abdulkhan94/HiFi-Audio-Amplifier-PCB_Design-/Documents & Simulations/FDR/proto_v2_1.png

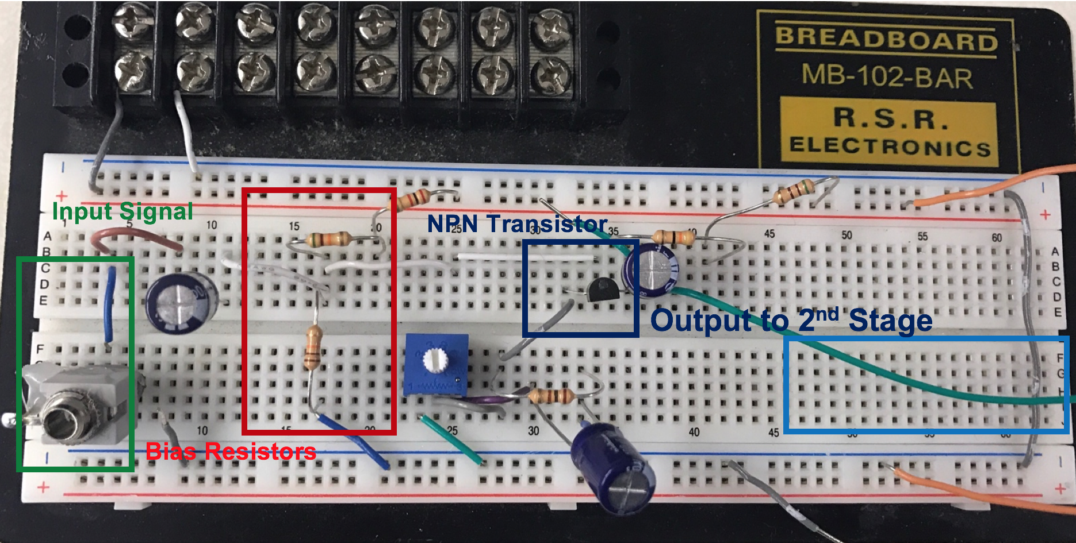
Documents & Simulations/FDR/proto_v2_1.png
