abdulkhan94/HiFi-Audio-Amplifier-PCB_Design-/Documents & Simulations/FDR/FFT_16.png

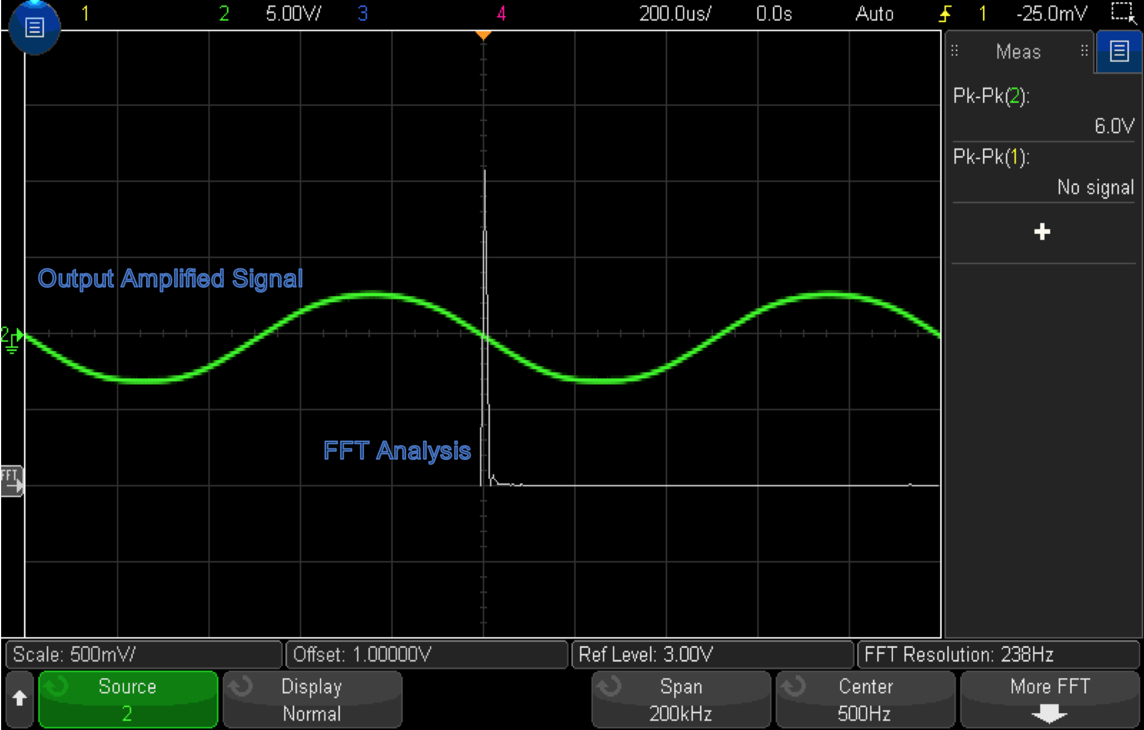
Documents & Simulations/FDR/FFT_16.png
