abdulkhan94/HiFi-Audio-Amplifier-PCB_Design-/Documents & Simulations/FDR/FFT_600.png

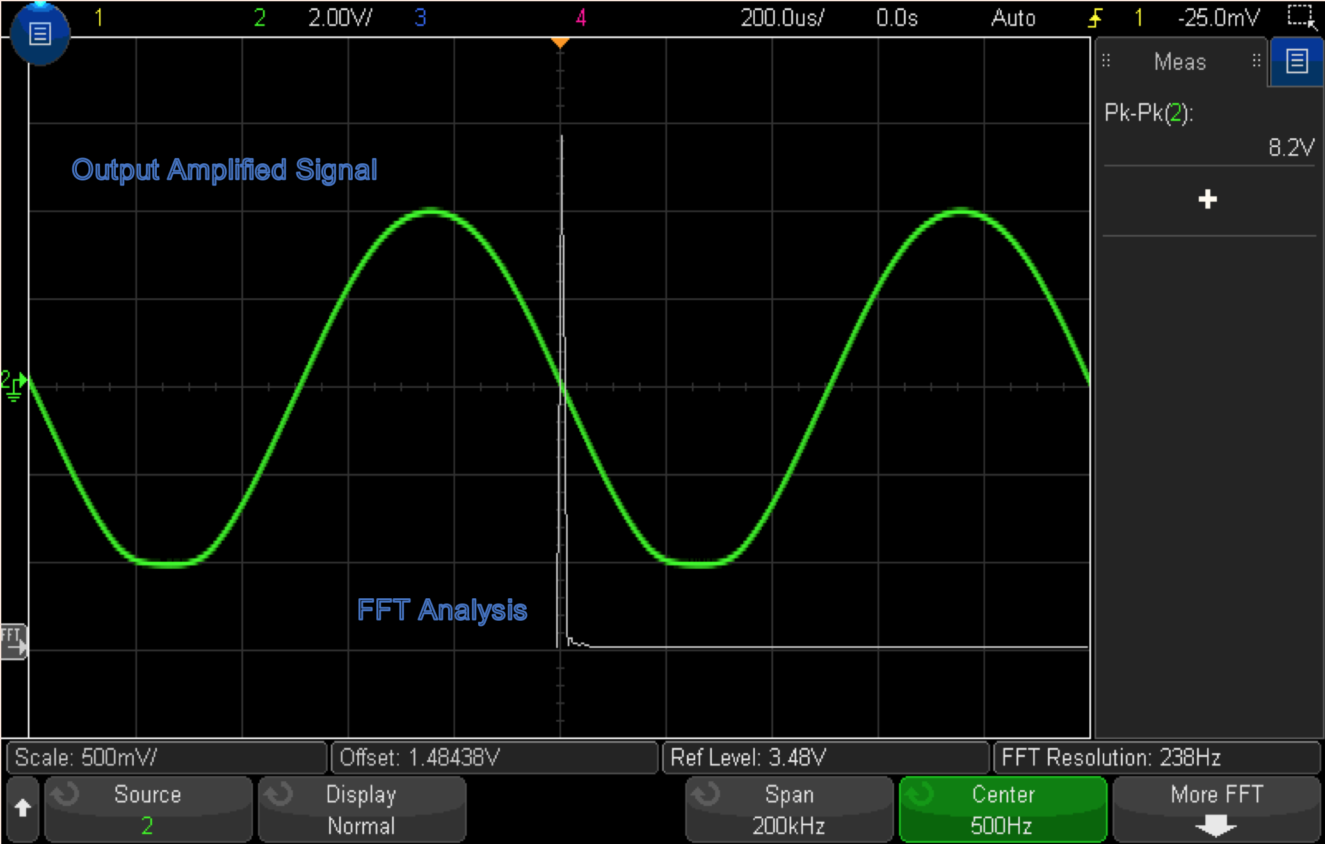
Documents & Simulations/FDR/FFT_600.png
