abdulkhan94/HiFi-Audio-Amplifier-PCB_Design-/Documents & Simulations/FDR/PCB_Final.png

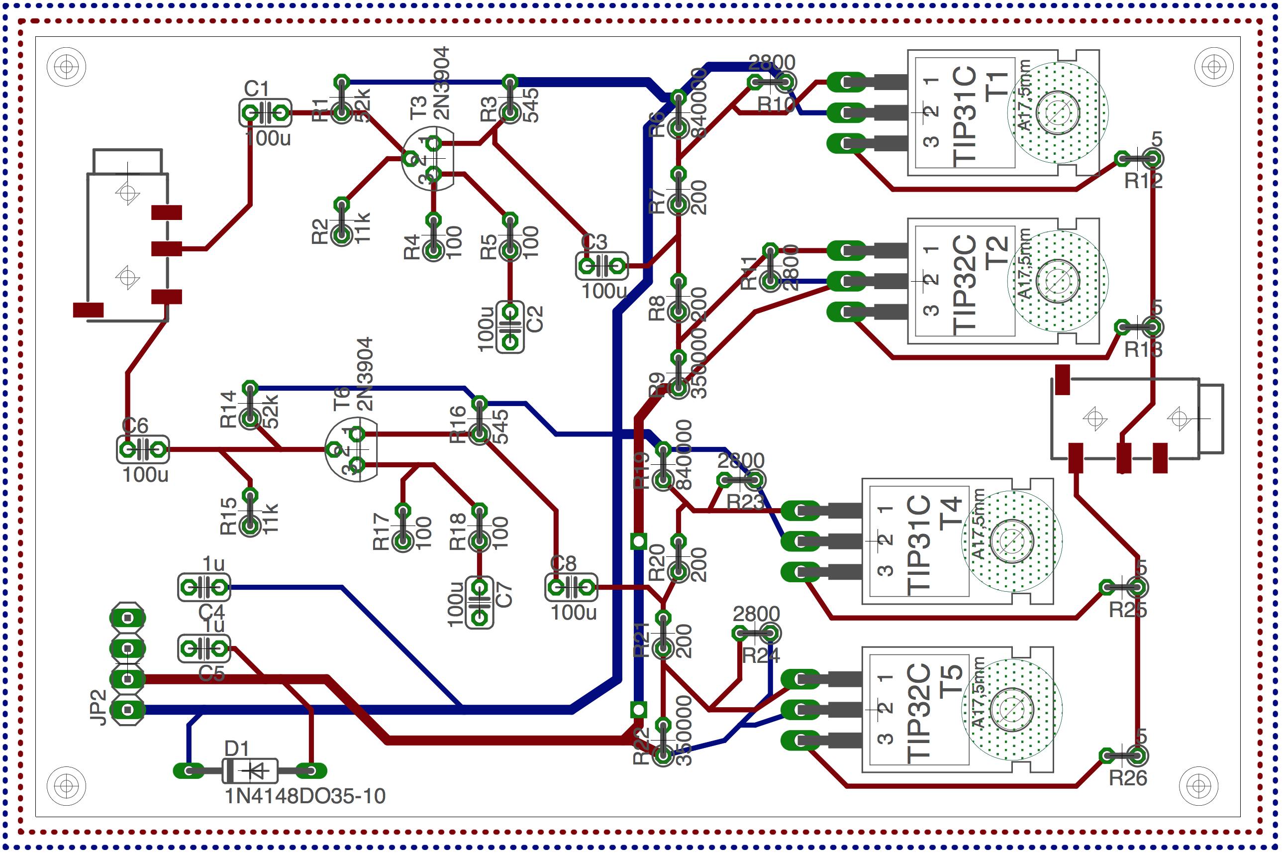
Documents & Simulations/FDR/PCB_Final.png
