abdulkhan94/HiFi-Audio-Amplifier-PCB_Design-/Documents & Simulations/FDR/Power_rails.png

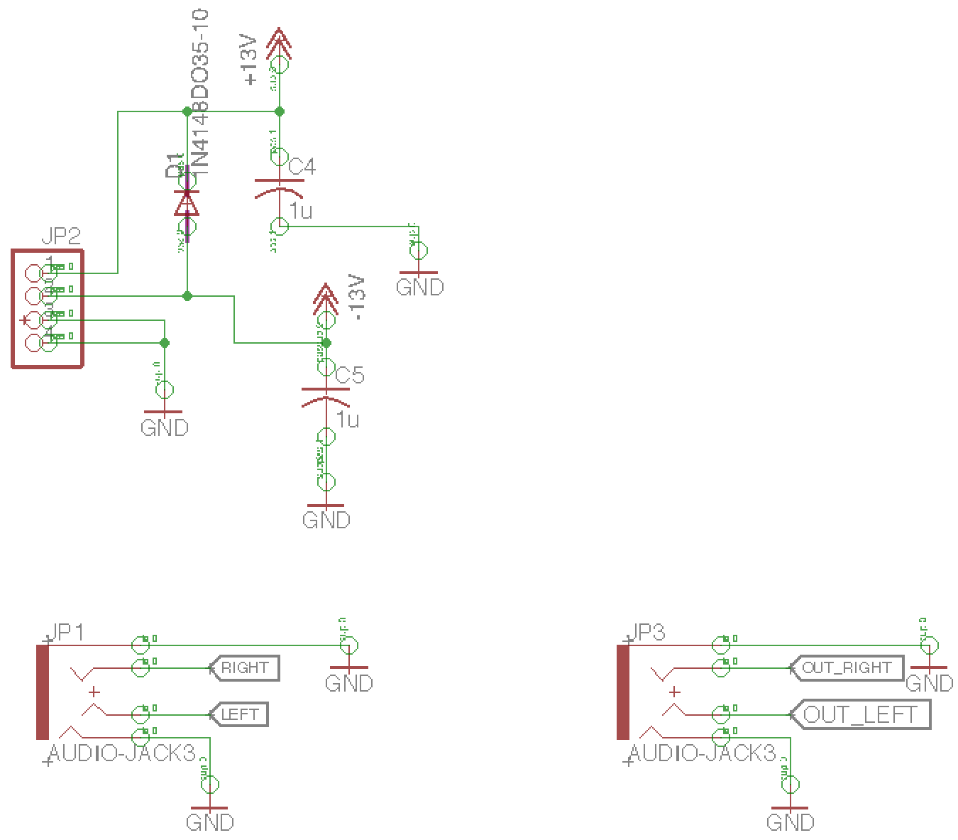
Documents & Simulations/FDR/Power_rails.png
