abdulkhan94/HiFi-Audio-Amplifier-PCB_Design-/Documents & Simulations/FDR/PowerAmp_300Hz.png

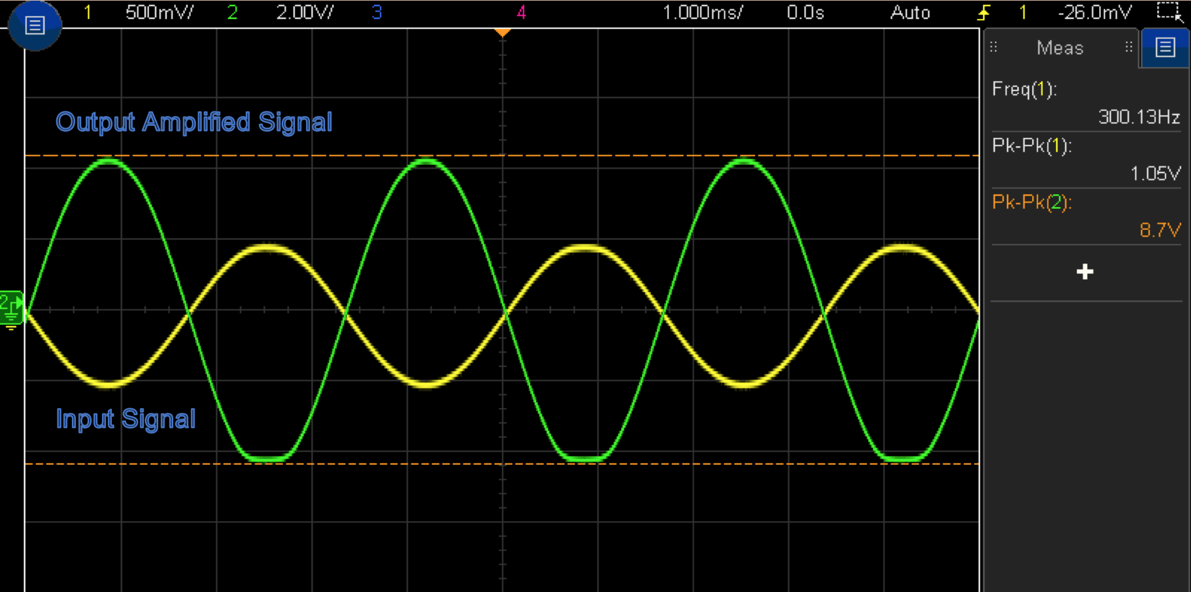
Documents & Simulations/FDR/PowerAmp_300Hz.png
