abdulkhan94/HiFi-Audio-Amplifier-PCB_Design-/Documents & Simulations/FDR/PowerAmp_600.png

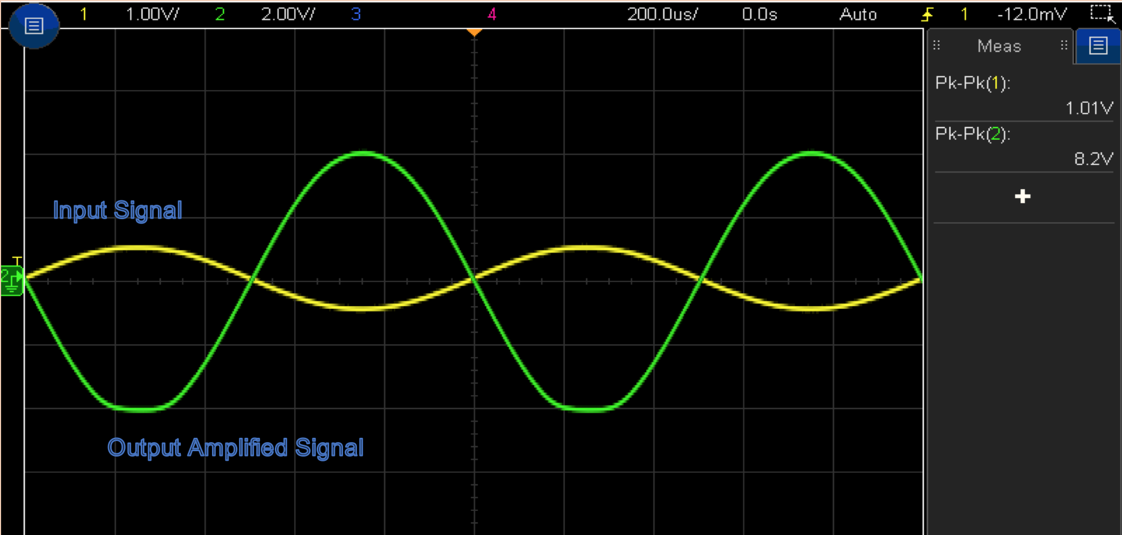
Documents & Simulations/FDR/PowerAmp_600.png
