abdulkhan94/HiFi-Audio-Amplifier-PCB_Design-/Documents & Simulations/FDR/Proto_anote1.png

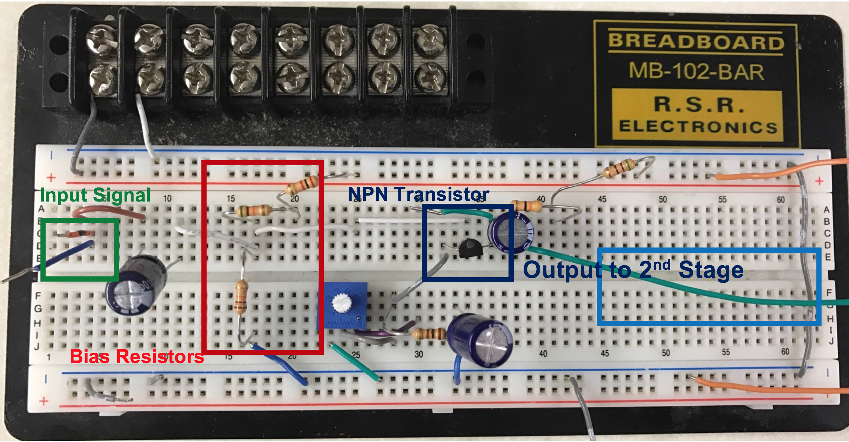
Documents & Simulations/FDR/Proto_anote1.png
