abdulkhan94/HiFi-Audio-Amplifier-PCB_Design-/Documents & Simulations/FDR/SlewRate.png

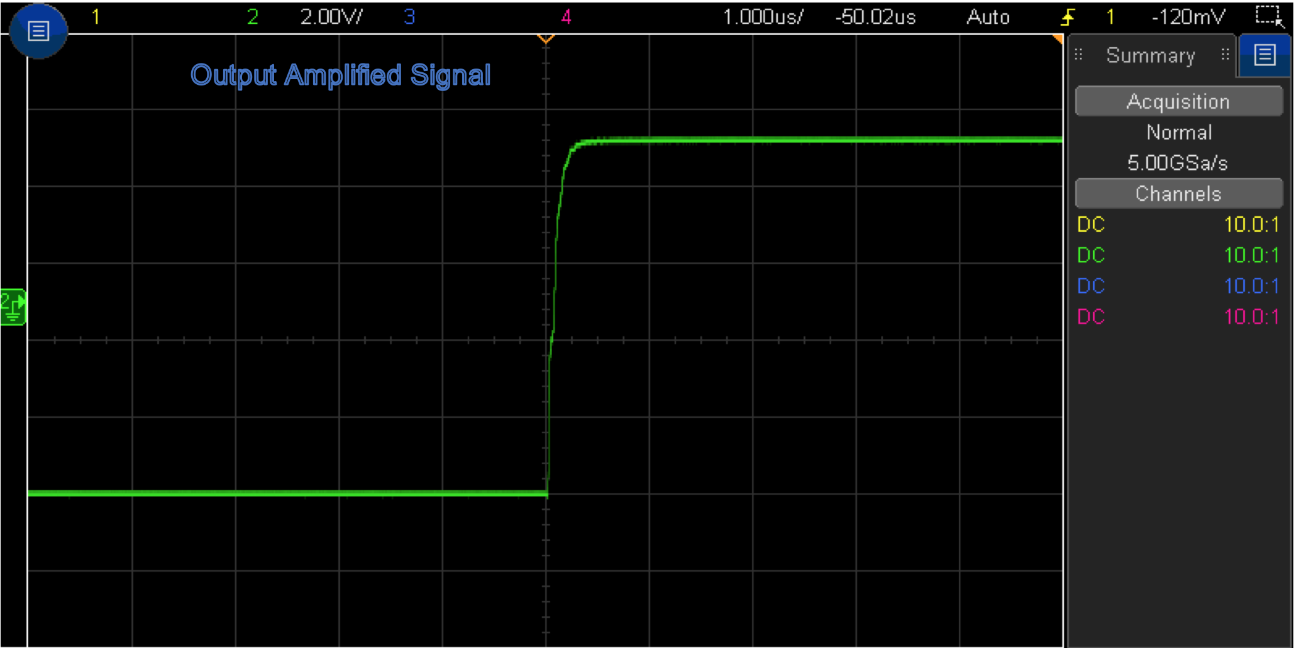
Documents & Simulations/FDR/SlewRate.png
