abdulkhan94/HiFi-Audio-Amplifier-PCB_Design-/Documents & Simulations/FDR/tip31c.png

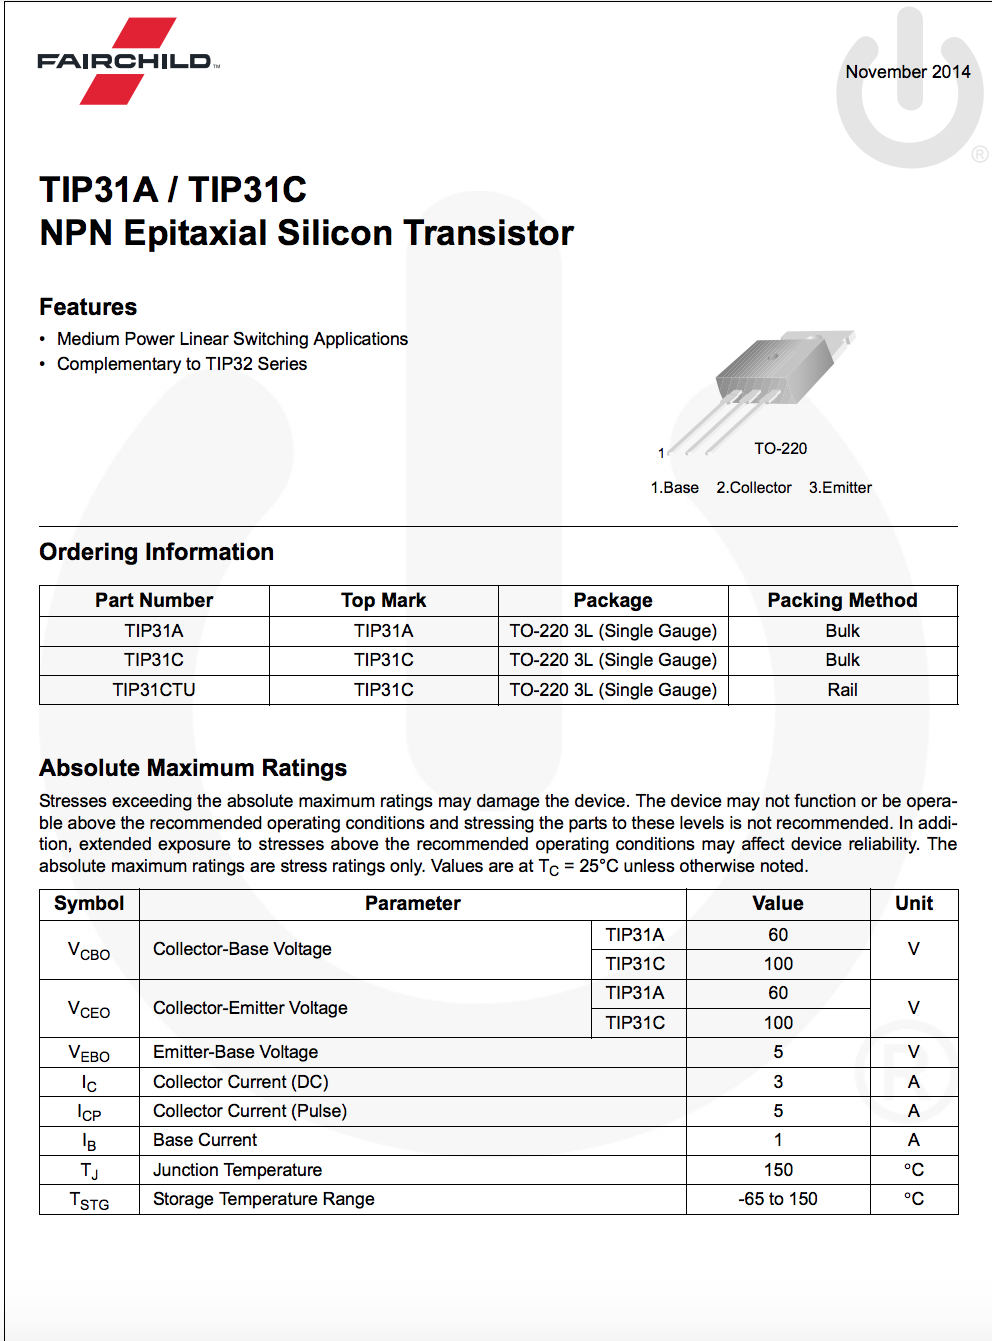
Documents & Simulations/FDR/tip31c.png
