abdulkhan94/HiFi-Audio-Amplifier-PCB_Design-/Documents & Simulations/Final Demo/PCB_Labelled.png

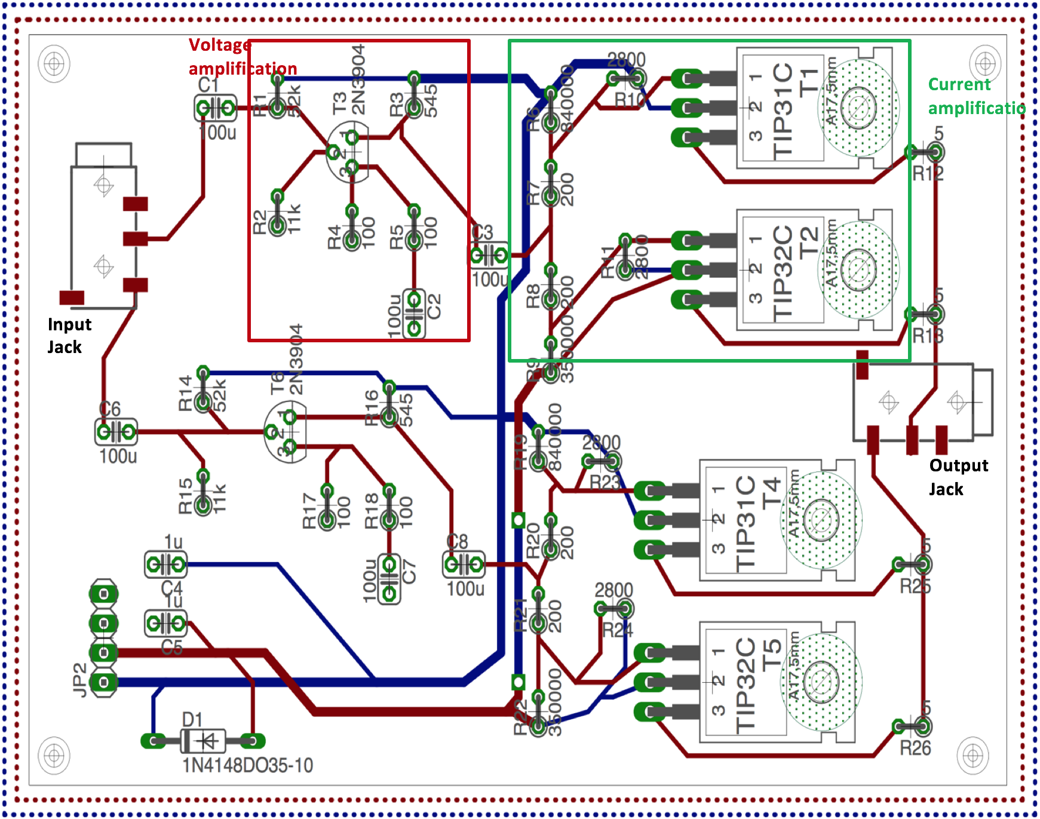
Documents & Simulations/Final Demo/PCB_Labelled.png
