abdulkhan94/HiFi-Audio-Amplifier-PCB_Design-/Documents & Simulations/ManagerMeeting2/Prototype_PowerAmp.png

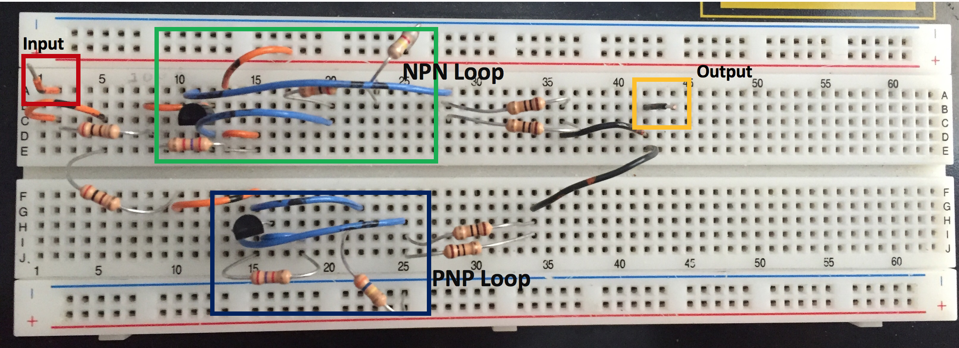
Documents & Simulations/ManagerMeeting2/Prototype_PowerAmp.png
