abdulkhan94/HiFi-Audio-Amplifier-PCB_Design-/Documents & Simulations/ManagerMeeting2/Prototype_VoltageAmp.png

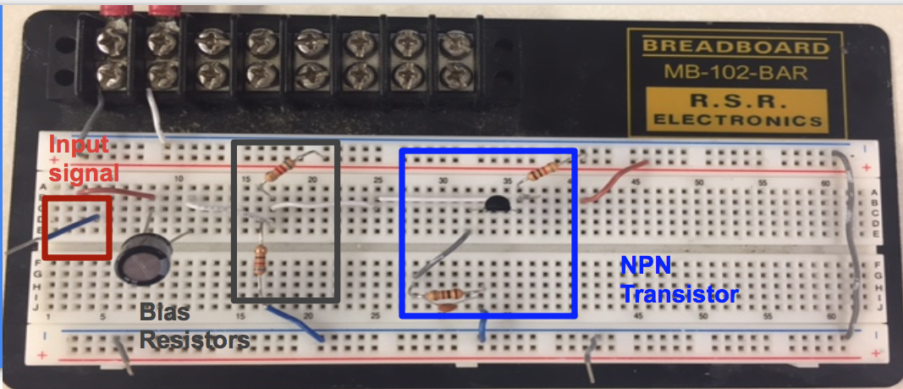
Documents & Simulations/ManagerMeeting2/Prototype_VoltageAmp.png
