abdulkhan94/HiFi-Audio-Amplifier-PCB_Design-/Documents & Simulations/MidTermSignoff/FFT_600.png

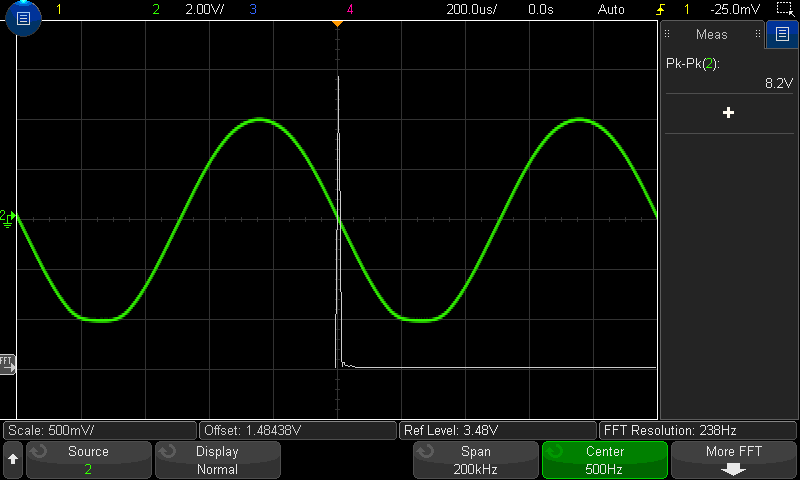
Documents & Simulations/MidTermSignoff/FFT_600.png
