abdulkhan94/HiFi-Audio-Amplifier-PCB_Design-/Documents & Simulations/MidTermSignoff/SlewRate.png

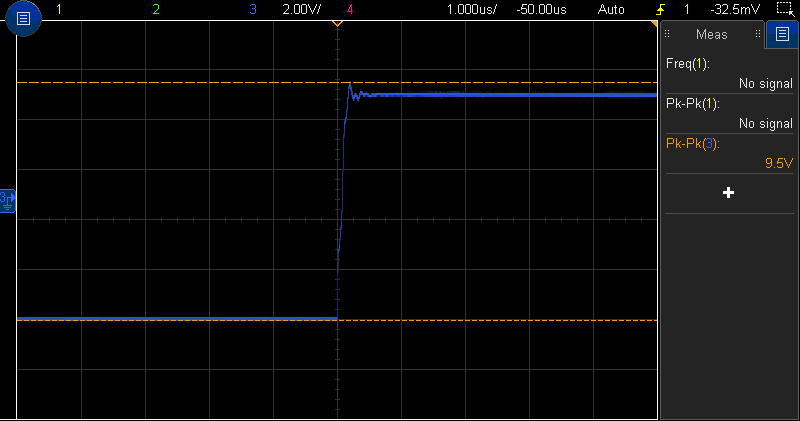
Documents & Simulations/MidTermSignoff/SlewRate.png
