abdulkhan94/HiFi-Audio-Amplifier-PCB_Design-/Documents & Simulations/Oscilloscope_PreAmp.jpeg

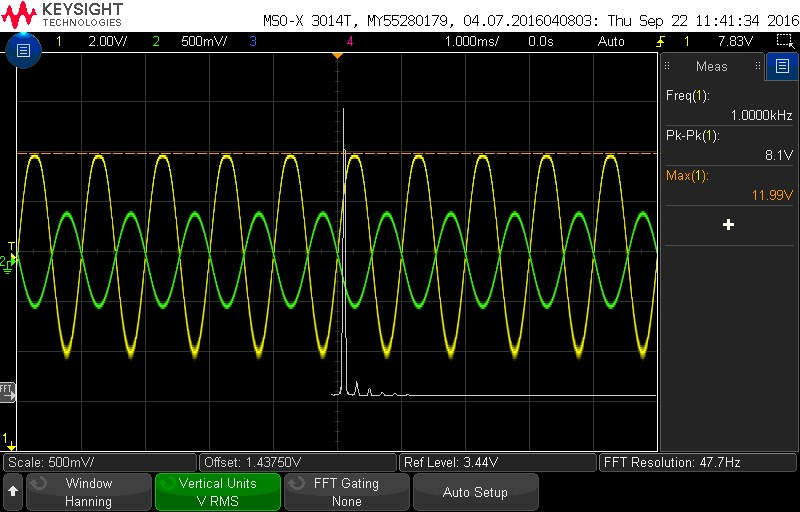
Documents & Simulations/Oscilloscope_PreAmp.jpeg
