abdulkhan94/HiFi-Audio-Amplifier-PCB_Design-/Documents & Simulations/PrototypePhoto.png

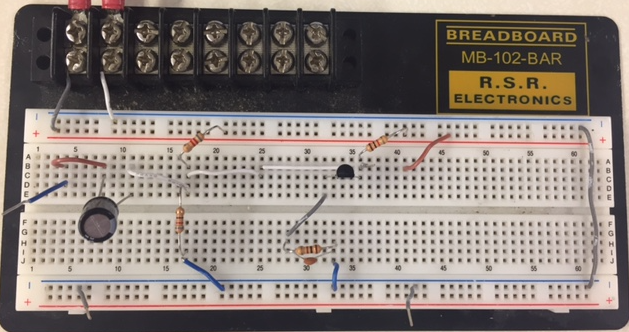
Documents & Simulations/PrototypePhoto.png
