abdulkhan94/HiFi-Audio-Amplifier-PCB_Design-/Documents & Simulations/Simulation_v1.png

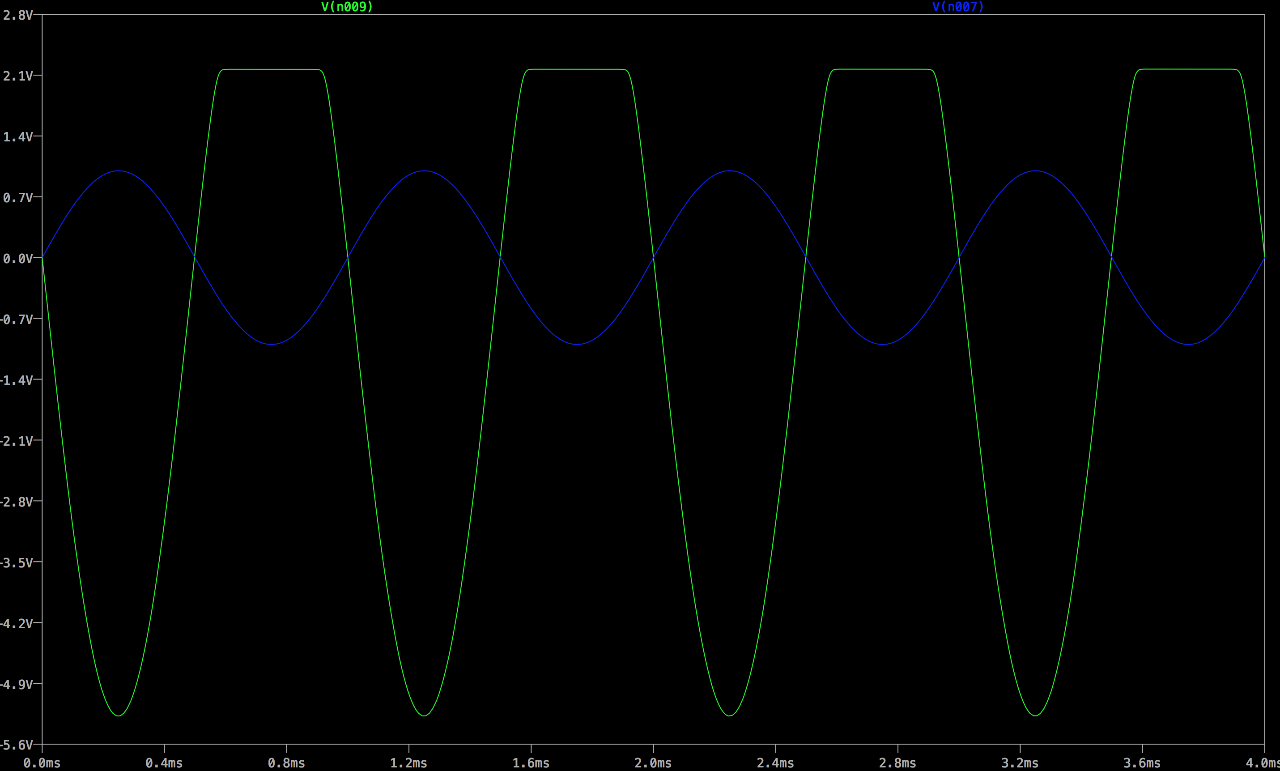
Documents & Simulations/Simulation_v1.png
