abdulkhan94/HiFi-Audio-Amplifier-PCB_Design-/Documents & Simulations/Scematic_v2.asc

C1: cap; 200µ
C2: cap; 500µ
C3: cap; 1.1µ
C4: cap; 100µ
D1: diode; 1N914
Q1: npn; 2N3904
Q2: npn; 2N3904
Q3: pnp; 2N3906
R1: res; 6k
R2: res; 10k
R3: res; 100
R4: res; 1k
R5: res; 500
R6: res; 840000
R7: res; 200
R8: res; 200
R9: res; 350000
R10: res; 2800
R11: res; 600
R12: res; 2800
R13: res; 5
R14: res; 5
V1: signal
V3: battery; 12
V4: battery; -12
V5: battery; 12
Named nets: 0
.tran 0 4ms 0
