abdulkhan94/HiFi-Audio-Amplifier-PCB_Design-/Documents & Simulations/Scematic_v4_curr.asc

C1: cap; 100µ
C2: cap; 100µ
C3: cap; 1.1µ
C4: cap; 100µ
D1: diode; 1N914
Q1: npn; 2N3904
Q4: npn; QTIP31C
Q5: pnp; QTIP32C
R1: res; 52k
R2: res; 11k
R3: res; 64
R4: res; 545
R5: res; 100
R6: res; 840000
R7: res; 200
R8: res; 200
R9: res; 350000
R10: res; 2800
R11: res; 600
R12: res; 2800
R13: res; 5
R14: res; 5
V1: signal; SINE(0 0.5 1K)
V3: battery; 13
V4: battery; -13
V5: battery; 13
Named nets: 0
.tran 0 4ms 0
.inc TIP31C.lib
.inc TIP32C.lib
